Kanrog/Rook-2020-Scalable/Images/Brick_v0_plate.PNG

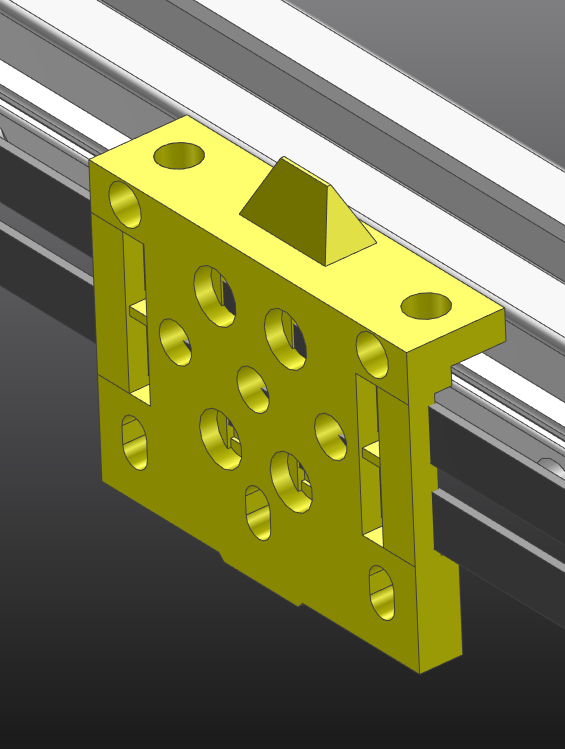
Images/Brick_v0_plate.PNG
