Kanrog/Rook-2020-Scalable/Images/Rookery.PNG

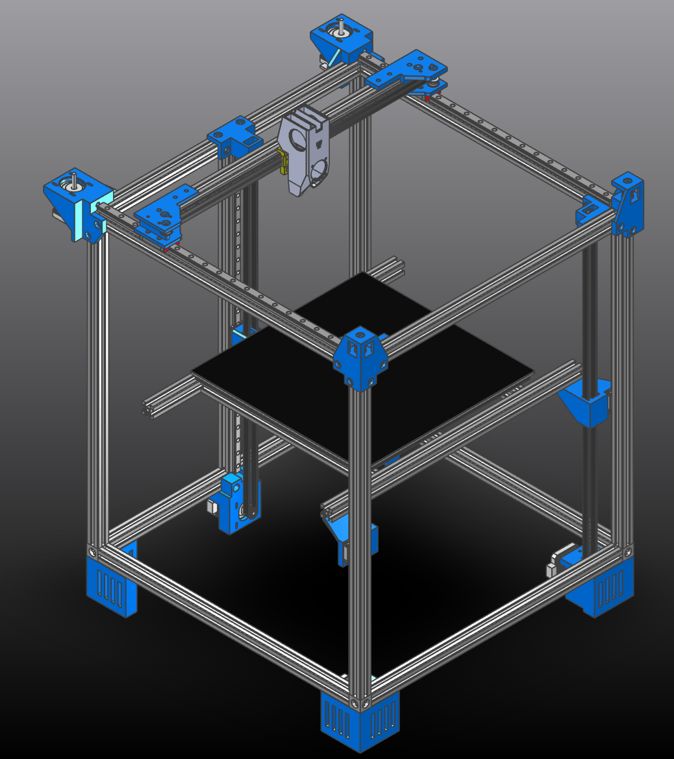
Images/Rookery.PNG
