Kanrog/Rook-2020-Scalable/Images/Rookery_bottom.PNG

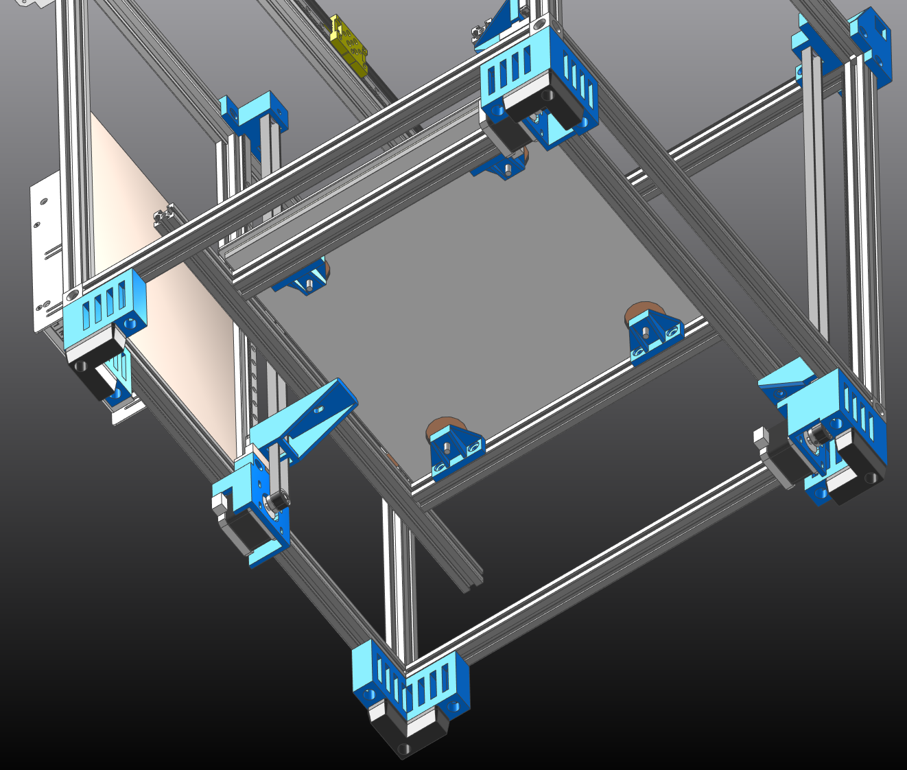
Images/Rookery_bottom.PNG
