Kanrog/Rook-2020-Scalable/Images/Rookery_key.PNG

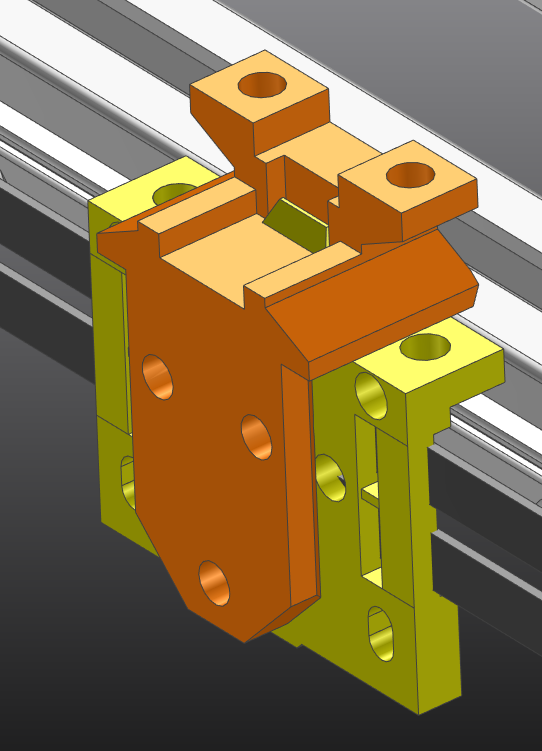
Images/Rookery_key.PNG
