Kanrog/Rook-2020-Scalable/STL/2x_Rear Feet.stl

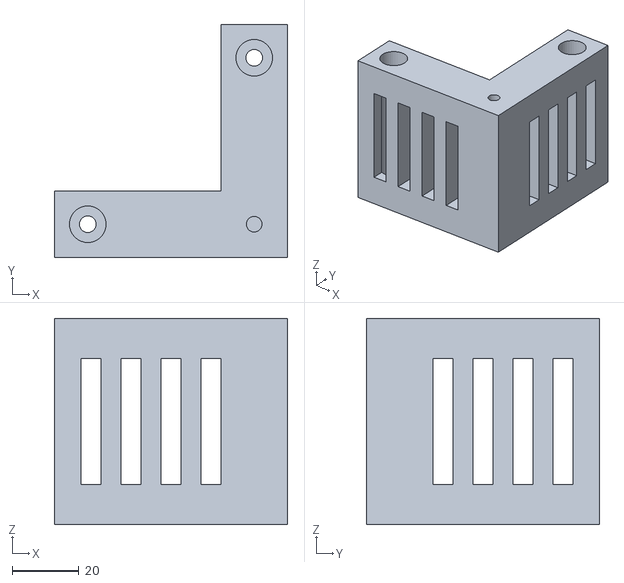
[picture p26: CAD file, 2023-05-20]
STL/2x_Rear Feet.stl
70.0 x 70.0 x 62.0
