Kanrog/Rook-2020-Scalable/STL/2x_Idler.stl

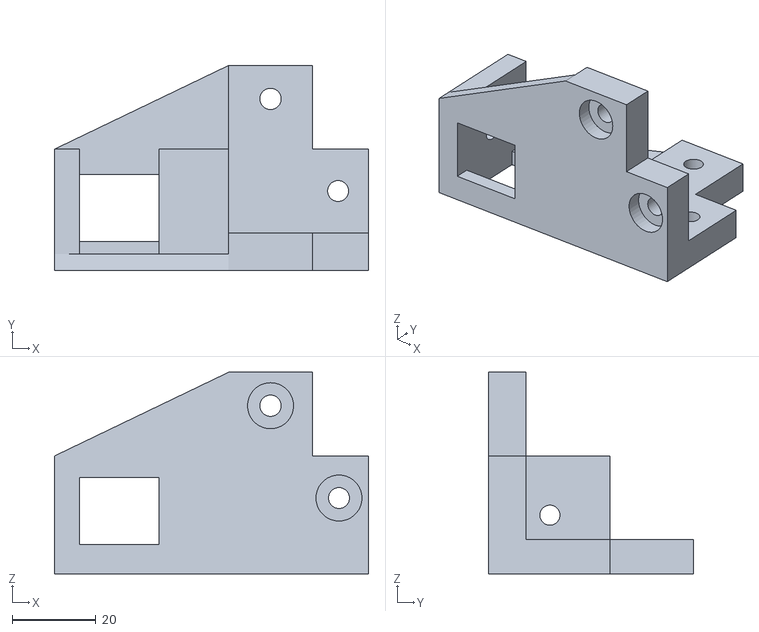
[picture p27: CAD file, 2023-05-20]
STL/2x_Idler.stl
75.0 x 49.0 x 48.1
