Kanrog/Rook-2020-Scalable/STL/4X_Bed-Mount.stl

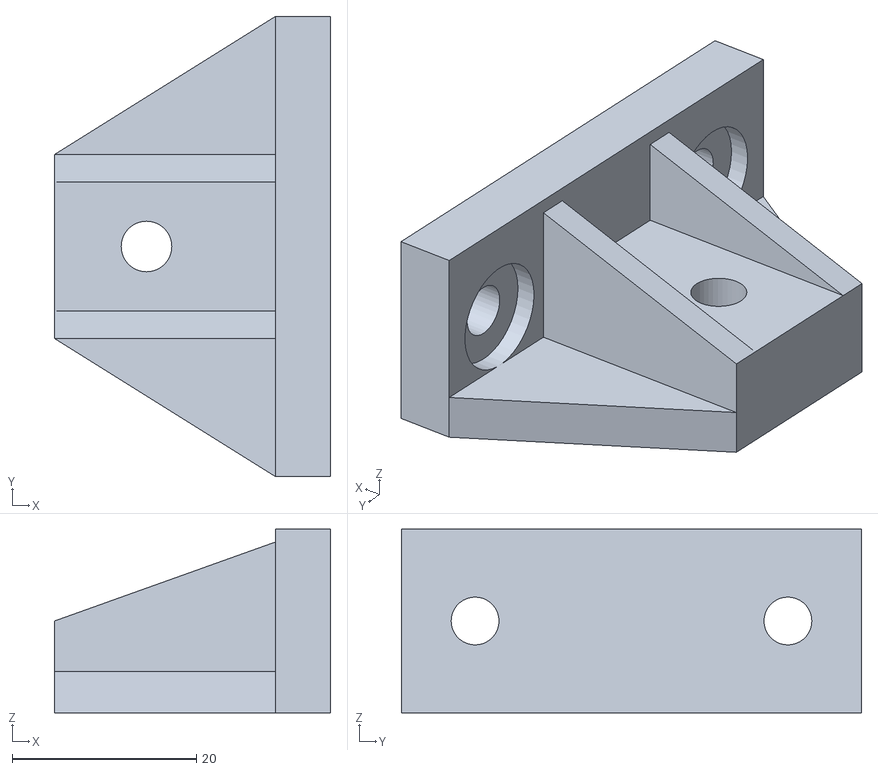
[picture p28: CAD file, 2023-05-20]
STL/4X_Bed-Mount.stl
30.0 x 50.0 x 20.0
