Kanrog/Rook-2020-Scalable/STL/1x_Motor Mount Right.stl

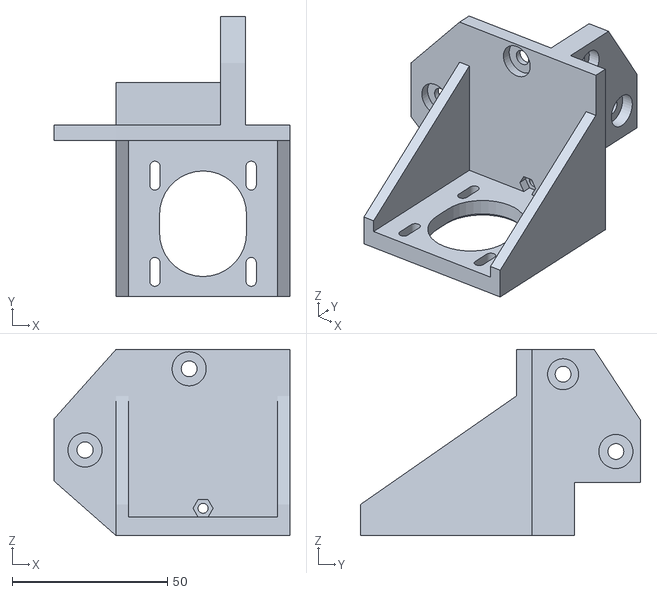
[picture p29: CAD file, 2023-05-20]
STL/1x_Motor Mount Right.stl
76.0 x 90.3 x 60.0
