Kanrog/Rook-2020-Scalable/Klipper Config/sensorless_homing_macro.cfg

[gcode_macro _HOME_X]
gcode:
    # Always use consistent run_current on A/B steppers during sensorless homing
    {% set RUN_CURRENT_X = printer.configfile.settings['tmc2209 stepper_x'].run_current|float %}
    {% set RUN_CURRENT_Y = printer.configfile.settings['tmc2209 stepper_y'].run_current|float %}
    {% set HOME_CURRENT = 0.65 %}
    SET_TMC_CURRENT STEPPER=stepper_x CURRENT={HOME_CURRENT}
    SET_TMC_CURRENT STEPPER=stepper_y CURRENT={HOME_CURRENT}

    # Home
    G28 X
    # Move away
    G91
    G1 X-10 F1200

#Wait just a second… (give StallGuard registers time to clear)
    G4 P1000
    # Set current during print
    SET_TMC_CURRENT STEPPER=stepper_x CURRENT={RUN_CURRENT_X}
    SET_TMC_CURRENT STEPPER=stepper_y CURRENT={RUN_CURRENT_Y}
    G90

[gcode_macro _HOME_Y]
gcode:
    # Set current for sensorless homing
    {% set RUN_CURRENT_X = printer.configfile.settings['tmc2209 stepper_x'].run_current|float %}
    {% set RUN_CURRENT_Y = printer.configfile.settings['tmc2209 stepper_y'].run_current|float %}
    {% set HOME_CURRENT = 0.65 %}
    SET_TMC_CURRENT STEPPER=stepper_x CURRENT={HOME_CURRENT}
    SET_TMC_CURRENT STEPPER=stepper_y CURRENT={HOME_CURRENT}

    # Home
    G28 Y
    # Move away
    G91
    G1 Y-10 F1200

#Wait just a second… (give StallGuard registers time to clear)
    G4 P1000
    # Set current during print
    SET_TMC_CURRENT STEPPER=stepper_x CURRENT={RUN_CURRENT_X}
    SET_TMC_CURRENT STEPPER=stepper_y CURRENT={RUN_CURRENT_Y}
   G90

[homing_override]
axes: xyz
gcode:
  {% set home_all = 'X' not in params and 'Y' not in params and 'Z' not in params %}

  {% if home_all or 'X' in params %}
    _HOME_X
  {% endif %}

  {% if home_all or 'Y' in params %}
    _HOME_Y
  {% endif %}

  {% if home_all or 'Z' in params %}
    G90
    G1 X150 Y115 F3000
    G28 Z
    G1 Z10
  {% endif %}
